Art4Tech/bc250-ronin-panel/display/external-originals/generated-images/exec-4da9aac9-0fe0-4da5-8608-f47c9597e4a3.png

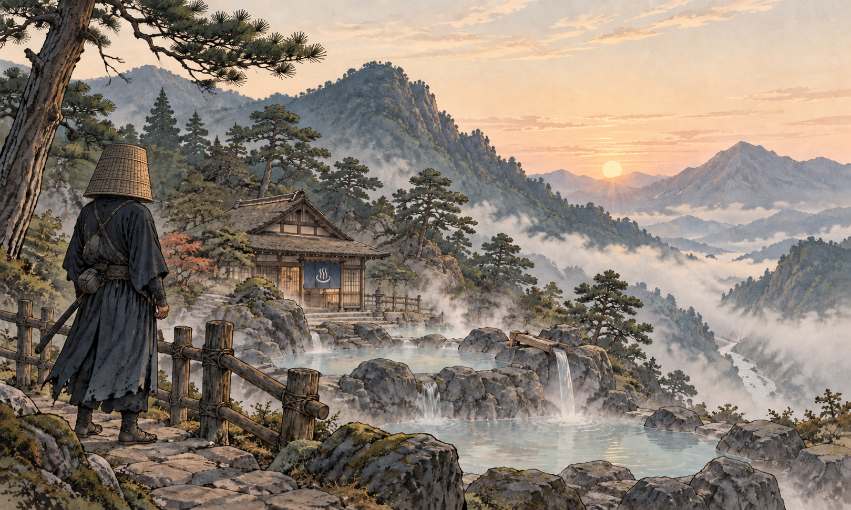
display/external-originals/generated-images/exec-4da9aac9-0fe0-4da5-8608-f47c9597e4a3.png
