Art4Tech/bc250-ronin-panel/display/external-originals/generated-images/exec-206e5a31-7dd7-47fe-836f-835abea814e2.png

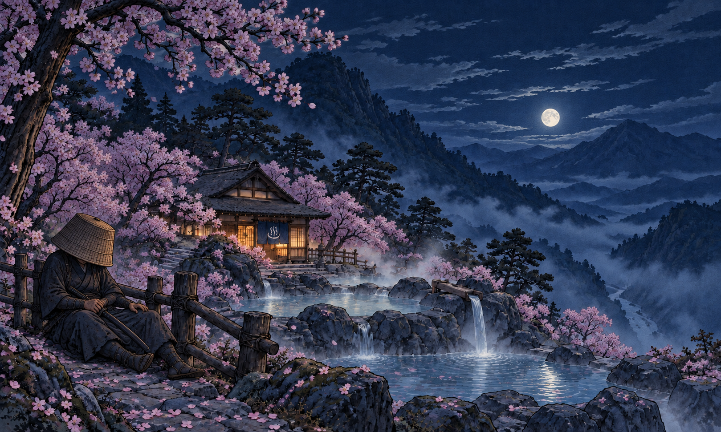
display/external-originals/generated-images/exec-206e5a31-7dd7-47fe-836f-835abea814e2.png
