Art4Tech/bc250-ronin-panel/display/external-originals/generated-images/exec-b12189bd-d82d-429f-b93b-6c578045d803.png

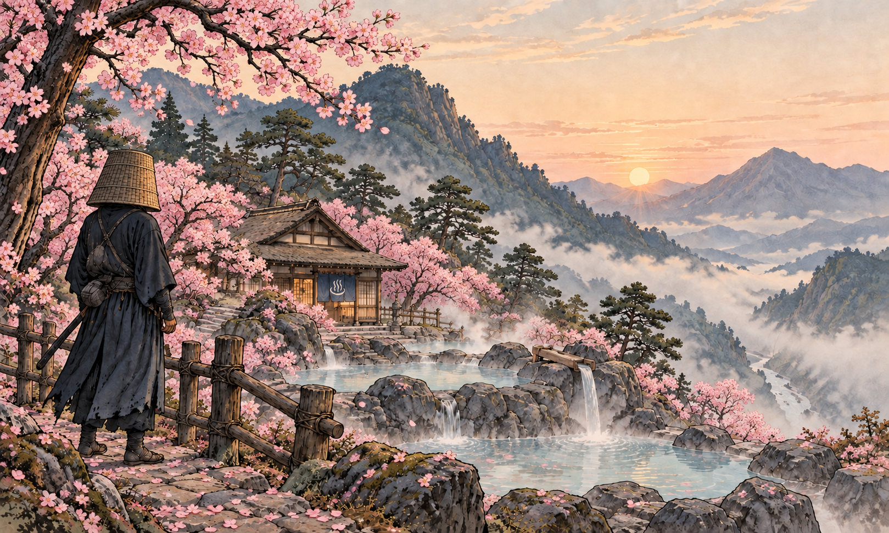
display/external-originals/generated-images/exec-b12189bd-d82d-429f-b93b-6c578045d803.png
