Art4Tech/bc250-ronin-panel/display/external-originals/generated-images/exec-ed61f22f-5310-4029-8da7-71df137390ba.png

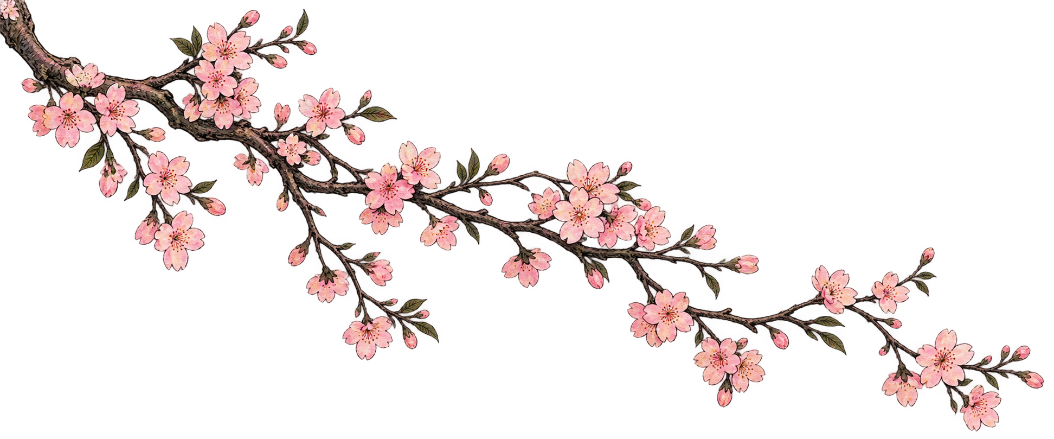
display/external-originals/generated-images/exec-ed61f22f-5310-4029-8da7-71df137390ba.png
