Art4Tech/bc250-ronin-panel/display/project/outputs/Resource-Panel/simulations/bazzite/bazzite-day-native.png

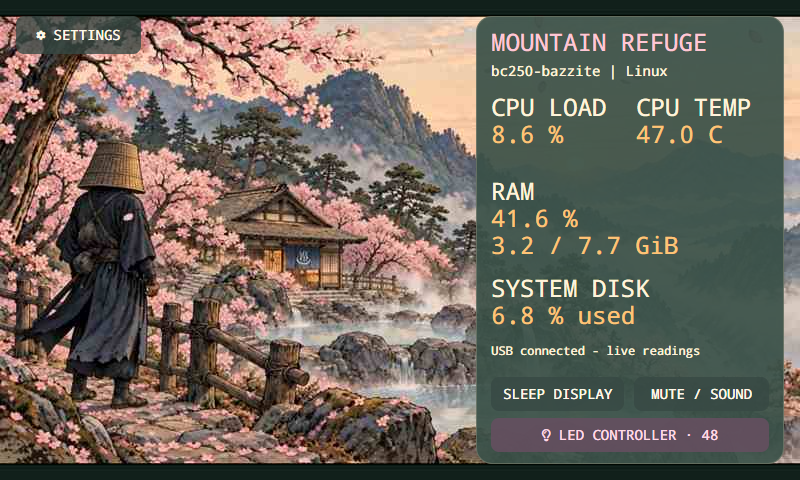
display/project/outputs/Resource-Panel/simulations/bazzite/bazzite-day-native.png
