Art4Tech/bc250-ronin-panel/display/project/outputs/Resource-Panel/simulations/bazzite/bazzite-led-controls.png

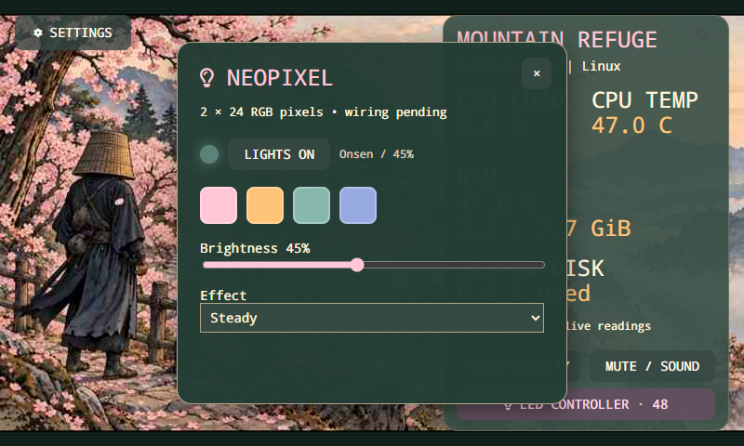
display/project/outputs/Resource-Panel/simulations/bazzite/bazzite-led-controls.png
