Art4Tech/bc250-ronin-panel/display/project/outputs/Resource-Panel/simulations/day-frame-2s.jpg

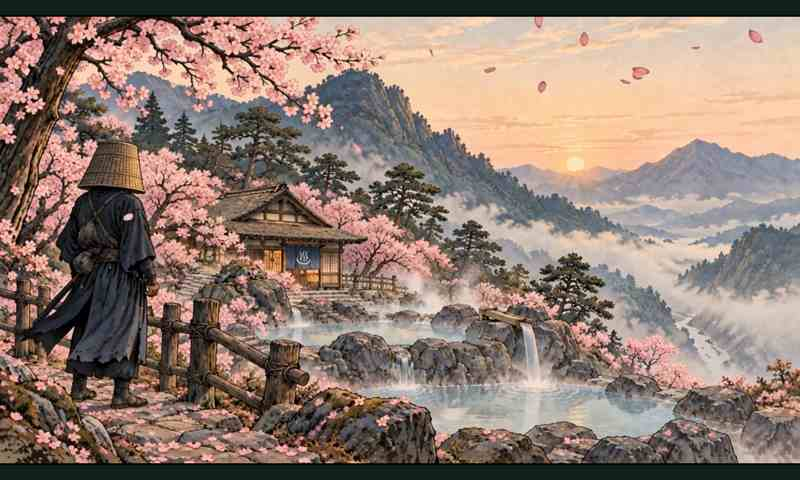
display/project/outputs/Resource-Panel/simulations/day-frame-2s.jpg
