Art4Tech/bc250-ronin-panel/display/project/outputs/Resource-Panel/video/movies-v3/dayidle-contact.jpg

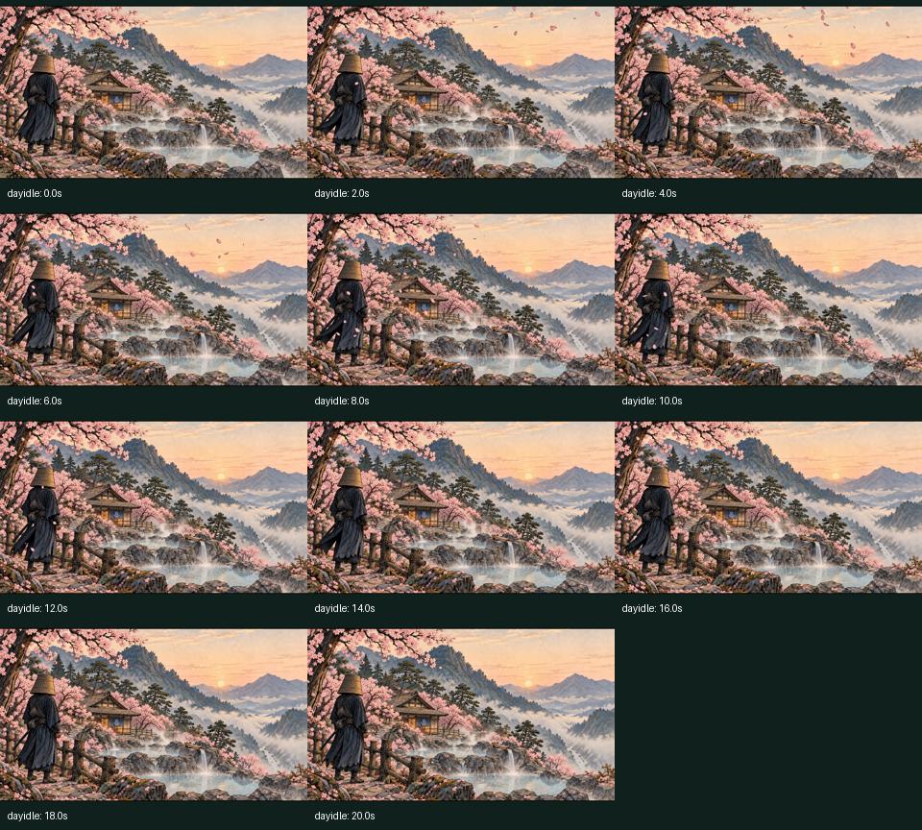
display/project/outputs/Resource-Panel/video/movies-v3/dayidle-contact.jpg
