Art4Tech/bc250-ronin-panel/display/project/outputs/Resource-Panel/video/user-clips/day-contact.jpg

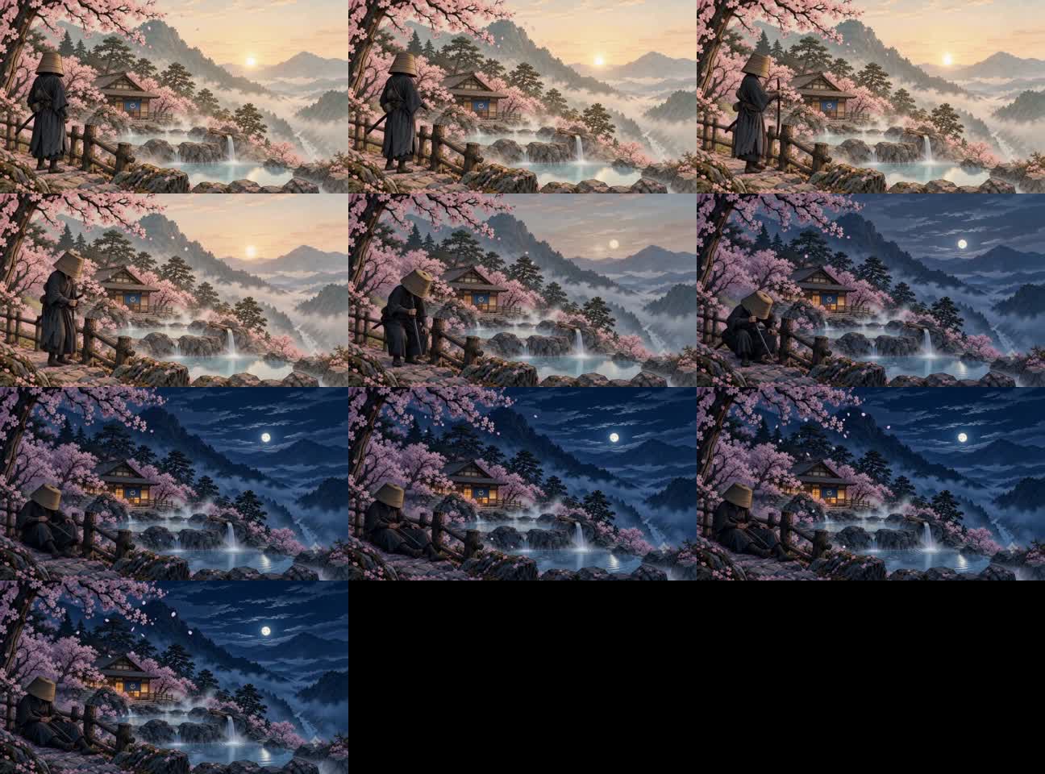
display/project/outputs/Resource-Panel/video/user-clips/day-contact.jpg
