Art4Tech/bc250-ronin-panel/display/project/outputs/Resource-Panel/video/user-clips/night-contact.jpg

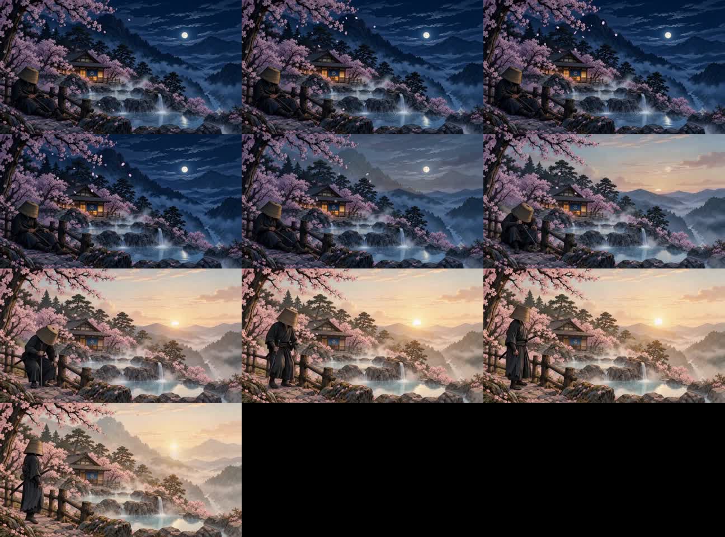
display/project/outputs/Resource-Panel/video/user-clips/night-contact.jpg
