Art4Tech/bc250-ronin-panel/display/project/outputs/Resource-Panel/windows-setup-qr.png

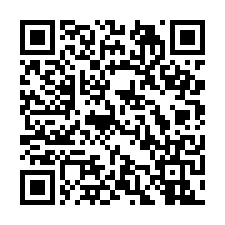
display/project/outputs/Resource-Panel/windows-setup-qr.png
